AlAminAshik/Multipurpose-Home-Automation-Socket-Using-Unihiker-K10/circuit/Main circuit V1.0/Main circuit V1.0.kicad_pcb

## KiCad design kicad/Electric Druid VCDO1.kicad_sch

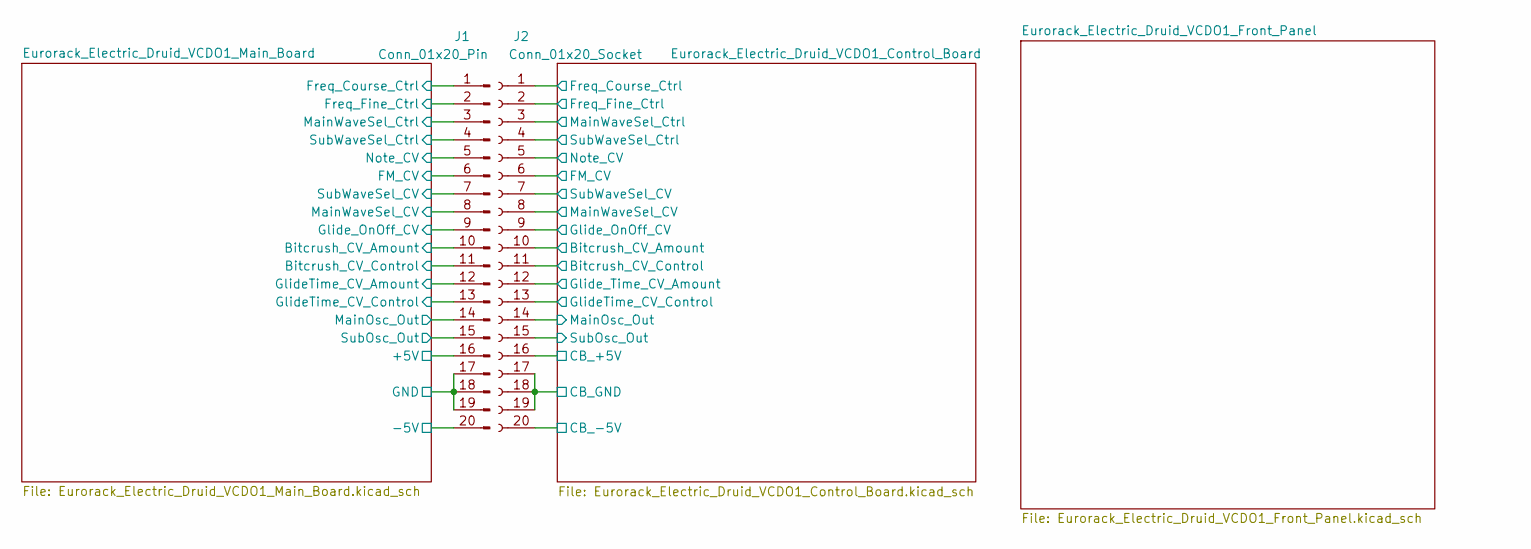
[picture p20: schematic Electric Druid VCDO1.kicad_sch]

Parts:
J1: Conn_01x20_Pin
J2: Conn_01x20_Socket

Connections:
+5V: J1.16
-5V: J1.20
Bitcrush_CV_Amount: J1.10, J2.10
Bitcrush_CV_Control: J1.11, J2.11
CB_+5V: J2.16
CB_-5V: J2.20
CB_GND: J2.17, J2.18, J2.19
FM_CV: J1.6, J2.6
Freq_Course_Ctrl: J1.1, J2.1
Freq_Fine_Ctrl: J1.2, J2.2
GND: J1.17, J1.18, J1.19
GlideTime_CV_Amount: J1.12
GlideTime_CV_Control: J1.13, J2.13
Glide_OnOff_CV: J1.9, J2.9
Glide_Time_CV_Amount: J2.12
MainOsc_Out: J1.14, J2.14
MainWaveSel_CV: J1.8, J2.8
MainWaveSel_Ctrl: J1.3, J2.3
Note_CV: J1.5, J2.5
SubOsc_Out: J1.15, J2.15
SubWaveSel_CV: J1.7, J2.7
SubWaveSel_Ctrl: J1.4, J2.4
