AlAminAshik/Multipurpose-Home-Automation-Socket-Using-Unihiker-K10/Main Code/include/alarmLogo.h

/* website to generate this array
https://notisrac.github.io/FileToCArray/
*/
#define ALARMCLOCKk_HEIGHT 137
#define ALARMCLOCKk_WIDTH 125

// array size is 34250
const uint8_t alarmclockk[] PROGMEM  = {
  0x00, 0x00, 0x00, 0x00, 0x00, 0x00, 0x00, 0x00, 0x00, 0x00, 0x00, 0x00, 0x00, 0x00, 0x00, 0x00, 0x00, 0x00, 0x00, 0x00, 0x00, 0x00, 0x00, 0x00, 0x00, 0x00, 0x00, 0x00, 0x00, 0x00, 0x00, 0x00, 0x00, 0x00, 0x00, 0x00, 0x00, 0x00, 0x00, 0x00, 0x00, 0x00, 0x00, 0x00, 0x00, 0x00, 0x00, 0x00, 0x00, 0x00, 0x00, 0x00, 0x00, 0x00, 0x00, 0x00, 0x00, 0x00, 0x00, 0x00, 0x00, 0x00, 0x00, 0x00, 0x00, 0x00, 0x00, 0x00, 0x00, 0x00, 0x00, 0x00, 0x00, 0x00, 0x00, 0x00, 0x00, 0x00, 0x00, 0x00, 0x00, 0x00, 0x00, 0x00, 0x00, 0x00, 0x00, 0x00, 0x00, 0x00, 0x00, 0x00, 0x00, 0x00, 0x00, 0x00, 0x00, 0x00, 0x00, 0x00, 0x00, 0x00, 0x00, 0x00, 0x00, 0x00, 0x00, 0x00, 0x00, 0x00, 0x00, 0x00, 0x00, 0x00, 0x00, 0x00, 0x00, 0x00, 0x00, 0x00, 0x00, 0x00, 0x00, 0x00, 0x00, 
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
  0xf1, 0x2a, 0x73, 0x2a, 0x73, 0x2a, 0x73, 0x2a, 0x73, 0x2a, 0x73, 0x2a, 0x73, 0x2a, 0x73, 0x2a, 0x73, 0x2a, 0x73, 0x2a, 0x73, 0x3a, 0xb2, 0x6b, 0xb0, 0x8c, 0x71, 0xa5, 0x55, 0xad, 0x55, 0xa5, 0x34, 0xa5, 0x14, 0x94, 0xb2, 0x8c, 0x71, 0x84, 0x30, 0x73, 0x8e, 0x6b, 0x4d, 0x5a, 0xeb, 0x52, 0x8a, 0x42, 0x28, 0x39, 0xc7, 0x31, 0xa6, 0x21, 0x24, 0x18, 0xc3, 0x10, 0xa2, 0x10, 0xa2, 0x10, 0x82, 0x10, 0x82, 0x08, 0x61, 0x08, 0x61, 0x08, 0x61, 0x08, 0x61, 0x08, 0x61, 0x08, 0x61, 0x10, 0x82, 0x10, 0x82, 0x10, 0xa3, 0x18, 0xc3, 0x18, 0xc3, 0x18, 0xe3, 0x21, 0x04, 0x29, 0x45, 0x31, 0xa7, 0x39, 0xe8, 0x2a, 0x52, 0x2a, 0x73, 0x2a, 0x73, 0x2a, 0x73, 0x2a, 0x73, 0x2a, 0x73, 0x2a, 0x73, 0x2a, 0x73, 0x2a, 0x73, 0x2a, 0x73, 0x2a, 0x73, 0x2a, 0x73, 0x2a, 0x73, 
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
};
