AlAminAshik/Multipurpose-Home-Automation-Socket-Using-Unihiker-K10/Main Code/include/ACIcon.h

#define AC_ICON_HEIGHT 40
#define AC_ICON_WIDTH 82

// array size is 6560
const uint8_t AC_icon[] PROGMEM  = {
  42, 115, 42, 115, 42, 115, 42, 115, 42, 115, 42, 115, 42, 115, 42, 115, 42, 115, 42, 115, 42, 115, 42, 115, 42, 115, 42, 115, 42, 115, 42, 115, 42, 115, 42, 115, 42, 115, 42, 115, 42, 115, 42, 115, 42, 115, 42, 115, 42, 115, 42, 115, 42, 115, 42, 115, 42, 115, 42, 115, 42, 115, 42, 115, 42, 115, 42, 115, 42, 115, 42, 115, 42, 115, 42, 115, 42, 115, 42, 115, 42, 115, 
  42, 115, 42, 115, 42, 115, 42, 115, 42, 115, 42, 115, 42, 115, 42, 115, 42, 115, 42, 115, 42, 115, 42, 115, 42, 115, 42, 115, 42, 115, 42, 115, 42, 115, 42, 115, 42, 115, 42, 115, 42, 115, 42, 115, 42, 115, 42, 115, 42, 115, 42, 115, 42, 115, 42, 115, 42, 115, 42, 115, 42, 115, 42, 115, 42, 115, 42, 115, 42, 115, 42, 115, 42, 115, 42, 115, 42, 115, 42, 115, 42, 115, 
  42, 115, 42, 115, 42, 115, 42, 115, 42, 115, 42, 115, 42, 115, 42, 115, 42, 115, 42, 115, 33, 206, 33, 206, 25, 74, 17, 41, 17, 41, 17, 41, 17, 41, 17, 41, 17, 41, 17, 41, 17, 41, 17, 41, 17, 41, 17, 41, 17, 41, 17, 41, 17, 41, 17, 41, 17, 41, 17, 41, 17, 41, 17, 41, 17, 41, 17, 41, 17, 41, 17, 41, 17, 41, 17, 41, 17, 41, 17, 41, 17, 41, 
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
};
