AlAminAshik/Multipurpose-Home-Automation-Socket-Using-Unihiker-K10/Main Code/include/fanIcon.h

#define FAN_ICON_HEIGHT 35
#define FAN_ICON_WIDTH 82

// array size is 5740
const uint8_t FAN_icon[] PROGMEM  = {
  42, 115, 42, 115, 42, 115, 42, 115, 42, 115, 42, 115, 42, 115, 42, 115, 42, 115, 42, 115, 42, 115, 42, 115, 42, 115, 42, 115, 42, 115, 42, 115, 42, 115, 42, 115, 42, 115, 42, 115, 42, 115, 42, 115, 42, 115, 42, 115, 42, 115, 42, 115, 42, 115, 42, 115, 42, 115, 42, 115, 42, 115, 42, 115, 42, 115, 42, 115, 42, 115, 42, 115, 42, 115, 42, 115, 42, 115, 42, 115, 42, 115, 
  42, 115, 42, 115, 42, 115, 42, 115, 42, 115, 42, 115, 42, 115, 42, 115, 42, 115, 42, 115, 42, 115, 42, 115, 42, 115, 42, 115, 42, 115, 42, 115, 42, 115, 42, 115, 42, 115, 42, 115, 42, 115, 42, 115, 42, 115, 42, 115, 42, 115, 42, 115, 42, 115, 42, 115, 42, 115, 42, 115, 42, 115, 42, 115, 42, 115, 42, 115, 42, 115, 42, 115, 42, 115, 42, 115, 42, 115, 42, 115, 42, 115, 
  42, 115, 42, 115, 42, 115, 42, 115, 42, 115, 42, 115, 42, 115, 42, 115, 42, 115, 42, 115, 42, 115, 42, 115, 42, 115, 42, 115, 42, 115, 42, 115, 42, 115, 42, 115, 42, 115, 42, 115, 42, 115, 42, 115, 42, 115, 42, 115, 42, 115, 42, 115, 42, 115, 42, 115, 42, 115, 42, 115, 42, 115, 42, 115, 42, 115, 42, 115, 42, 115, 42, 115, 42, 115, 42, 115, 42, 115, 42, 115, 42, 115, 
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
  85, 120, 85, 120, 85, 120, 85, 120, 85, 120, 85, 120, 85, 120, 17, 37, 8, 65, 0, 32, 8, 130, 75, 109, 83, 239, 83, 239, 125, 215, 75, 143, 67, 45, 108, 244, 142, 155, 142, 155, 150, 221, 150, 188, 159, 95, 167, 159, 167, 127, 167, 127, 167, 127, 167, 127, 167, 127, 167, 127, 167, 127, 167, 127, 167, 127, 167, 127, 167, 127, 167, 127, 167, 127, 150, 253, 0, 0, 0, 0, 17, 41, 
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
};
