AlAminAshik/Multipurpose-Home-Automation-Socket-Using-Unihiker-K10/Main Code/include/lightIcon.h

#define LIGHT_ICON_HEIGHT 40
#define LIGHT_ICON_WIDTH 86

// array size is 6880
const uint8_t light_icon[] PROGMEM  = {
  42, 115, 42, 115, 42, 115, 42, 115, 42, 115, 42, 115, 42, 115, 42, 115, 42, 115, 42, 115, 42, 115, 42, 115, 42, 115, 42, 115, 42, 115, 42, 115, 42, 115, 42, 115, 42, 115, 42, 115, 42, 115, 42, 115, 42, 115, 42, 115, 42, 115, 42, 115, 42, 115, 42, 115, 42, 115, 42, 115, 42, 115, 42, 115, 42, 115, 42, 115, 42, 115, 42, 115, 42, 115, 42, 50, 25, 140, 17, 41, 25, 140, 42, 50, 42, 115, 
  42, 115, 42, 115, 42, 115, 42, 115, 42, 115, 42, 115, 42, 115, 42, 115, 42, 115, 42, 115, 42, 115, 42, 115, 42, 115, 42, 115, 42, 115, 42, 115, 42, 115, 42, 115, 42, 115, 42, 115, 42, 115, 42, 115, 42, 115, 42, 115, 42, 115, 42, 115, 42, 115, 42, 115, 42, 115, 42, 115, 42, 115, 42, 115, 42, 115, 42, 115, 42, 115, 42, 115, 42, 115, 42, 115, 42, 115, 42, 115, 42, 115, 42, 115, 42, 115, 
  42, 115, 42, 115, 42, 115, 42, 115, 42, 115, 42, 115, 42, 115, 42, 115, 42, 115, 42, 115, 42, 115, 42, 115, 42, 115, 42, 115, 42, 115, 42, 115, 42, 115, 42, 115, 42, 115, 42, 115, 42, 115, 42, 115, 42, 115, 42, 115, 42, 115, 42, 115, 42, 115, 42, 115, 42, 115, 42, 115, 42, 115, 42, 115, 42, 115, 42, 115, 42, 115, 42, 115, 34, 17, 0, 33, 0, 0, 0, 0, 0, 0, 0, 33, 42, 50, 
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
};
