AlAminAshik/Multipurpose-Home-Automation-Socket-Using-Unihiker-K10/Main Code/include/GreenOnSwitchIcon.h

#define GREENBUTTON_HEIGHT 27
#define GREENBUTTON_WIDTH 85

// array size is 4590
const uint8_t greenbutton[] PROGMEM  = {
  0x2a, 0x73, 0x2a, 0x73, 0x2a, 0x73, 0x2a, 0x73, 0x2a, 0x73, 0x2a, 0x73, 0x2a, 0x73, 0x2a, 0x73, 0x2a, 0x73, 0x2a, 0x73, 0x2a, 0x73, 0x2a, 0xb2, 0x23, 0x11, 0x23, 0x11, 0x23, 0x11, 0x23, 0x11, 0x23, 0x11, 0x23, 0x11, 0x23, 0x11, 0x23, 0x11, 0x23, 0x11, 0x23, 0x11, 0x23, 0x11, 0x23, 0x11, 0x23, 0x11, 0x23, 0x11, 0x23, 0x11, 0x23, 0x11, 0x23, 0x11, 0x23, 0x11, 0x23, 0x11, 0x23, 0x11, 0x23, 0x11, 0x23, 0x11, 0x23, 0x11, 0x23, 0x11, 0x23, 0x11, 0x23, 0x11, 0x23, 0x11, 0x23, 0x11, 0x23, 0x11, 0x23, 0x11, 0x23, 
  0x11, 0x23, 0x11, 0x23, 0x11, 0x23, 0x11, 0x23, 0x11, 0x23, 0x11, 0x23, 0x11, 0x23, 0x11, 0x23, 0x11, 0x23, 0x11, 0x23, 0x11, 0x23, 0x11, 0x23, 0x11, 0x23, 0x11, 0x23, 0x11, 0x23, 0x11, 0x23, 0x11, 0x23, 0x11, 0x23, 0x11, 0x23, 0x11, 0x23, 0x11, 0x23, 0x11, 0x23, 0x11, 0x23, 0x11, 0x23, 0x11, 0x23, 0x11, 0x23, 0x11, 0x23, 0x11, 0x23, 0x11, 0x23, 0x11, 0x23, 0x11, 0x23, 0x11, 0x2a, 0x92, 0x2a, 0x73, 0x2a, 0x73, 0x2a, 0x73, 0x2a, 0x73, 0x2a, 0x73, 0x2a, 0x73, 0x2a, 0x73, 0x2a, 0x73, 0x2a, 0x73, 0x2a, 0x73, 
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
};
