AlAminAshik/Multipurpose-Home-Automation-Socket-Using-Unihiker-K10/Main Code/include/RedOffSwitchIcon.h

#define RED_OFF_SWITCH_HEIGHT 27
#define RED_OFF_SWITCH_WIDTH 85

// array size is 12656
const uint8_t Red_off_switch[] PROGMEM  = {
    0x2a, 0x73, 0x2a, 0x73, 0x2a, 0x73, 0x2a, 0x73, 0x2a, 0x73, 0x2a, 0x73, 0x2a, 0x73, 0x2a, 0x73, 0x2a, 0x73, 0x2a, 0x73, 0x2a, 0x73, 0x52, 0x10, 0x5a, 0x0f, 0x5a, 0x0f, 0x5a, 0x0f, 0x5a, 0x0f, 0x5a, 0x0f, 0x5a, 0x0f, 0x5a, 0x0f, 0x5a, 0x0f, 0x5a, 0x0f, 0x5a, 0x0f, 0x5a, 0x0f, 0x5a, 0x0f, 0x5a, 0x0f, 0x5a, 0x0f, 0x5a, 0x0f, 0x5a, 0x0f, 0x5a, 0x0f, 0x5a, 0x0f, 0x5a, 0x0f, 0x5a, 0x0f, 0x5a, 0x0f, 0x5a, 0x0f, 0x5a, 0x0f, 0x5a, 0x0f, 0x5a, 0x0f, 0x5a, 0x0f, 0x5a, 0x0f, 0x5a, 0x0f, 0x5a, 0x0f, 0x5a, 0x0f, 0x5a, 
  0x0f, 0x5a, 0x0f, 0x5a, 0x0f, 0x5a, 0x0f, 0x5a, 0x0f, 0x5a, 0x0f, 0x5a, 0x0f, 0x5a, 0x0f, 0x5a, 0x0f, 0x5a, 0x0f, 0x5a, 0x0f, 0x5a, 0x0f, 0x5a, 0x0f, 0x5a, 0x0f, 0x5a, 0x0f, 0x5a, 0x0f, 0x5a, 0x0f, 0x5a, 0x0f, 0x5a, 0x0f, 0x5a, 0x0f, 0x5a, 0x0f, 0x5a, 0x0f, 0x5a, 0x0f, 0x5a, 0x0f, 0x5a, 0x0f, 0x5a, 0x0f, 0x5a, 0x0f, 0x5a, 0x0f, 0x5a, 0x0f, 0x5a, 0x0f, 0x5a, 0x0f, 0x5a, 0x0f, 0x3a, 0x52, 0x2a, 0x73, 0x2a, 0x73, 0x2a, 0x73, 0x2a, 0x73, 0x2a, 0x73, 0x2a, 0x73, 0x2a, 0x73, 0x2a, 0x73, 0x2a, 0x73, 0x2a, 0x73, 
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
};
